indietyp/IoP/sensor_scripts/extensions/led/moisture_bar.py

import time
from models.plant import Plant
from tools.main import VariousTools
from models.sensor import Sensor, SensorStatus
from sensor_scripts.driver.mcp23017 import MCP230XX_GPIO


class MoistureBar:
  def __init__(self):
    pass

  @staticmethod
  def run():
    result = VariousTools.offline_check('ledbar', hardware=True, pins=[0, 1, 2, 3, 4, 5], mcp=True)
    if result:
      sensor = Sensor.get(Sensor.name == 'moisture')
      plant = Plant.get(localhost=True)
      status = SensorStatus.get(SensorStatus.sensor == sensor,
                                SensorStatus.plant == plant)

      bus = 1
      gpio_count = 16
      address = 0x20

      mcp = MCP230XX_GPIO(bus, address, gpio_count)

      # green color port: 2, 1
      # yellow color port: 4, 3
      # red color port: 6, 5
      led = 0
      for i in [['threat', 6, 5], ['cautioning', 4, 3], ['optimum', 2, 1]]:
        if status.level.label == i[0]:
          led = i[2] if status.status is True else i[1]

      pins = [0, 1, 2, 3, 4, 5]
      for pin in pins:
        mcp.setup(pin, mcp.OUT)

      for i in range(0, led - 1):
        mcp.output(i, 0)  # Pin Low
        time.sleep(round((1.35**i) / 10, 3))

      for i in range(5, led - 2, -1):
        mcp.output(i, 1)  # Pin High
        time.sleep(round((1.35**i) / 10, 3))


if __name__ == "__main__":
  MoistureBar.run()
