indietyp/IoP/sensor_scripts/driver/mcp3002.py

import spidev


class mcp3002:
  def __init__(self):
    pass

  def readadc(self, device=0, channel=0):
    if device not in [1, 0] or channel not in [1, 0]:
      return -1

    spi = spidev.SpiDev()
    spi.open(0, device)

    command = [1, (2 + channel) << 6, 0]
    reply = spi.xfer2(command)

    value = reply[1] & 31
    value = value << 6

    value = value + (reply[2] >> 2)
    spi.close()

    return value

  def read_pct(self, device=0, channel=0):
    r = mcp3002.readadc(device, channel)
    return int(round((r / 1023.0) * 100))

  def read_3v3(self, device=0, channel=0):
    r = mcp3002.readadc(device, channel)
    v = (r / 1023.0) * 3.3
    return v

  def readadc_avg(self, device=0, channel=0):
    r = []
    for i in range(0, 10):
      r.append(mcp3002.readadc(device, channel))
    return sum(r) / 10.0
